clementleger/brewomatic/sw/BrewOMatic/HeaterControl.cpp

#include "HeaterControl.h"
#include "SerialOutput.h"
#include "Config.h"


HeaterControl::HeaterControl(unsigned int sampleTime):
mPidOutput(0),
mCtrl(),
mEnable(0),
mTargetTemp(0),
mPidInput(0),
mPid(&mPidInput, &mPidOutput, &mTargetTemp, PID_P_VALUE, PID_I_VALUE, PID_D_VALUE, DIRECT)
{
	mPid.SetOutputLimits(0, 100);
	mPid.SetSampleTime(sampleTime);
}

void HeaterControl::setEnable(bool enable)
{
	if (enable) {
		if (mEnable)
			return;

		mPidOutput = 0;
		mTargetTemp = 0;
		mPid.SetMode(AUTOMATIC);
		mCtrl.enable(true);
	} else {
		if (!mEnable)
			return;
		mPid.SetMode(MANUAL);
		mCtrl.enable(false);
	}

	mEnable = enable;
}

void HeaterControl::setTargetTemp(double targetTemp)
{
	mTargetTemp = targetTemp;
	
}

void HeaterControl::handleHeating(double currentTemp)
{
	int ret;

	mPidInput = currentTemp;
	ret = mPid.Compute();
	if (ret) {
		dbgOutput("PID output: %d\n", (int) mPidOutput);
		mCtrl.setDutyCycle((unsigned char) mPidOutput);
	}
}
