clementleger/brewomatic/sw/BrewOMatic/RotaryEncoder.h

#ifndef _ROTARY_ENCODER_H
#define _ROTARY_ENCODER_H

#include "Input.h"
#include <Encoder.h>

class RotaryEncoder: public Input {
	public:
		RotaryEncoder();
		char getButtonPressed();
	private:
		Encoder encoder;
		long oldPosition;
};

#endif /* _ROTARY_ENCODER_H */
