clementleger/brewomatic/sw/BrewOMatic/BrewOMatic.h

#ifndef _BREWOMATIC_H
#define _BREWOMATIC_H

#include "Config.h"

#define MAX_STR_SIZE	30

#define SEC_TO_MS(_sec)	(_sec * 1000)

#define BREWOMATIC_VERSION_STRING	"0.2"

class BrewOMatic;

#include "Input.h"
#include "Beeper.h"
#include "Recipe.h"
#include "Language.h"
#include "IdleInfo.h"
#include "SDHandling.h"
#include "TempDS18B20.h"
#include "TempMax31865.h"
#include "SerialOutput.h"
#include "DisplayUcglib.h"
#include "RotaryEncoder.h"
#include "HeaterControl.h"
#include "DisplayLiquidCrystal.h"

typedef enum {
	SUCCESS = 0,
	ERROR_RECIPE_EXECUTON_FAILED,
	ERROR_USER_CANCELLED,
} brewomaticError;

typedef enum {
	STATE_IDLE,
	STATE_BREWING,
	STATE_MANUAL,
} brewomaticState;

typedef enum {
	BREWING_GET_NEXT_STEP,
	BREWING_PRE_STEP_ACTION,
	BREWING_START_STEP,
	BREWING_WAIT_TEMP_REACHED,
	BREWING_WAIT_END_OF_STEP,
	BREWING_END,
} brewingState;

class BrewOMatic {
	public:
		void setup();
		void run();
		BrewOMatic();

		/* Callbacks */
		void actionStopBrewing();
		void actionStartBrewing();
		void actionStartManual();
		void actionNextStep();
		bool actionEnablePump();
		void actionMenuBack(bool exit);
		void setCurrentMenu(Menu *m);
		float mCurrentTemp;

		Recipe *mCurrentRecipe;
		Step *mCurrentStep;
		Action *mCurrentAction;

		HeaterControl *mHeaterControl;
		unsigned long mStepStartMillis;
		unsigned int mTargetTemp;
		brewStringIndex mStatus;
		bool mError;
	private:
		brewomaticState mState;

		TEMP_PROBE_TYPE mTempProbe;
		DISPLAY_TYPE mDisp;
		RotaryEncoder mInput;

		unsigned long mLastDispUpdate;
		unsigned long mTempUpdate;
		unsigned long mLastBeepTime;
#if ENABLED(STAT_OUTPUT)
		unsigned long mLastStatUpdate;
#endif
		void setTargetTemp(unsigned int);
		void setError(brewStringIndex err);
		void setTempOnButton(unsigned char b);

		brewingState mBrewingState;
		Menu *mCurrentMenu;
		Menu *mIdleMenu;
		Menu *mBrewingMenu;
		bool mUpdateDisplay;

		void getNextStep();
		void startStep();
		void waitEndOfStep();
		void waitTempReached();
		void waitUserAction();
		void brewingEnd();

		void updateTemp();
		void updateDisplay();
		void updateStat();

		void changeState(brewomaticState state);
		void handleIdle();
		void handleBrewing();
		void handleMenu();
		void handleManual();

		void handleDisplay();
		void displayMenu();
		unsigned char handleButton(Menu *onPress);
};

#endif
