clementleger/brewomatic/sw/BrewOMatic/Recipe.h

#ifndef _RECIPE_H
#define _RECIPE_H

#define MAX_STEP_COUNT		10
#define MAX_USER_ACTION_COUNT	4

#include "Language.h"
#include "List.h"

class Action {
	public:
		Action(brewStringIndex descIdx, unsigned long time):
		mDescIdx(descIdx),
		mTime(time) {};

		Action(brewStringIndex descIdx):
		mDescIdx(descIdx) {};

		brewStringIndex getDescIdx() {return mDescIdx;};
	private:
		brewStringIndex mDescIdx;
		unsigned long mTime;
};

class Step {
	public:
		~Step();
		Step();
		Step(brewStringIndex name, unsigned long duration,
		     unsigned char targetTemp, bool enablePump,
		     unsigned char mPumpDutyCycle,
		     unsigned char actionCount);

		bool mEnablePump;
		unsigned char mPumpDutyCycle;
		unsigned char mTargetTemp;
		unsigned long mDuration;
		brewStringIndex mName;

		/* Action to be run before executing the step */
		Action *mPreStepAction;
		/* List of user action requiring confirmation
		 * during brewing */
		List<Action *> mUserActions;
};

class Recipe {
	public:
		~Recipe();
		Recipe(unsigned char stepCount, const char *name);

		List<Step *> mSteps;
		char *mName;
};

Step *createManualStep();

#endif
