clementleger/brewomatic/sw/BrewOMatic/Macros.h

#ifndef _MACROS_H
#define _MACROS_H

#define STRINGIFY_(M) #M
#define STRINGIFY(M) STRINGIFY_(M)

#define LANGUAGE_INCL_(M) STRINGIFY_(lang/Lang##M.h)
#define LANGUAGE_INCL(M) LANGUAGE_INCL_(M)
#define INCLUDE_LANGUAGE LANGUAGE_INCL(DISP_LANGUAGE)

// Macros to support option testing
#define _CAT(a, ...) a ## __VA_ARGS__
#define SWITCH_ENABLED_false 0
#define SWITCH_ENABLED_true  1
#define SWITCH_ENABLED_0     0
#define SWITCH_ENABLED_1     1
#define SWITCH_ENABLED_      1
#define ENABLED(b) _CAT(SWITCH_ENABLED_, b)

#endif
